dpicken/atari-hw/pdf/gtia-interposer-layout.pdf

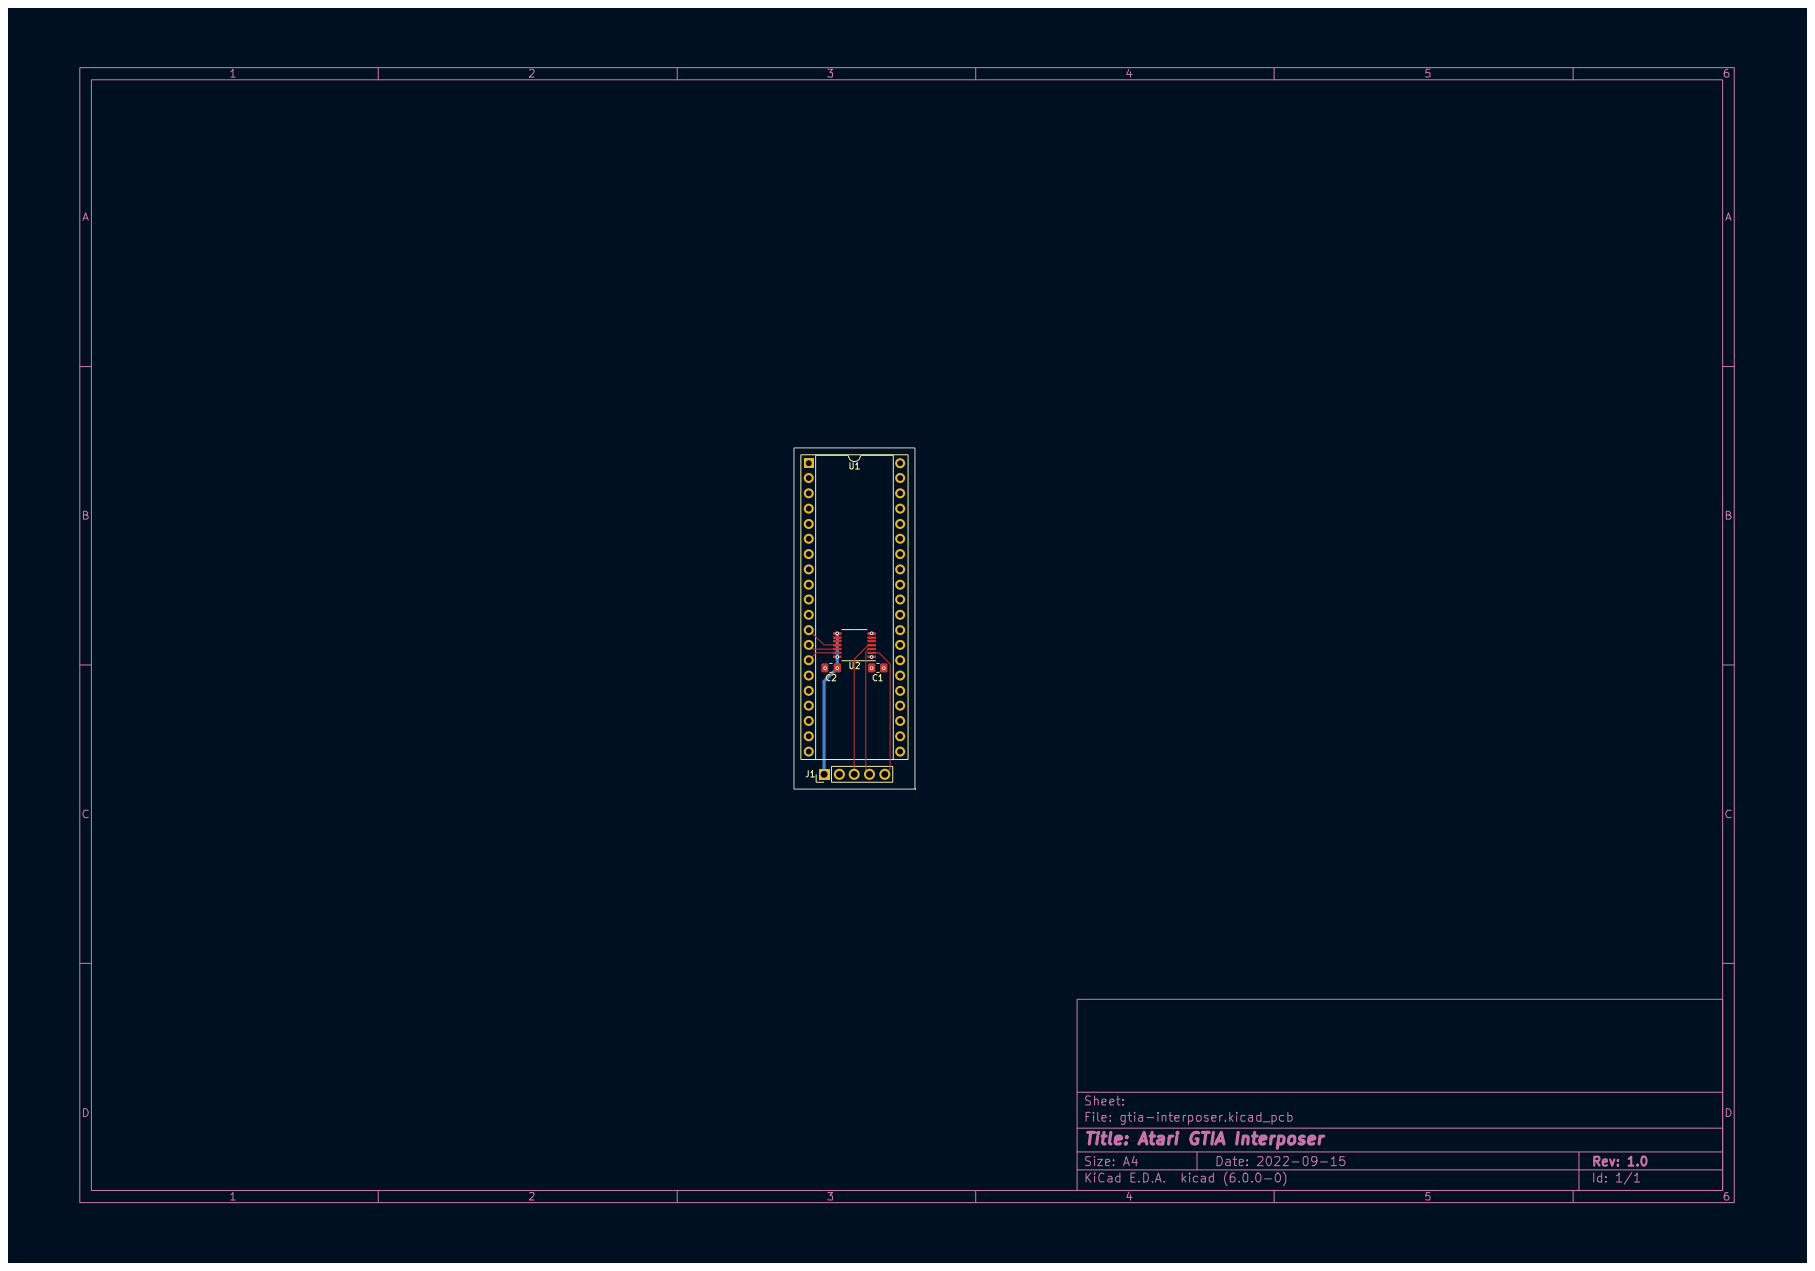
[picture p34: page 1]
