dpicken/atari-hw/pdf/pokey-interposer-layout.pdf

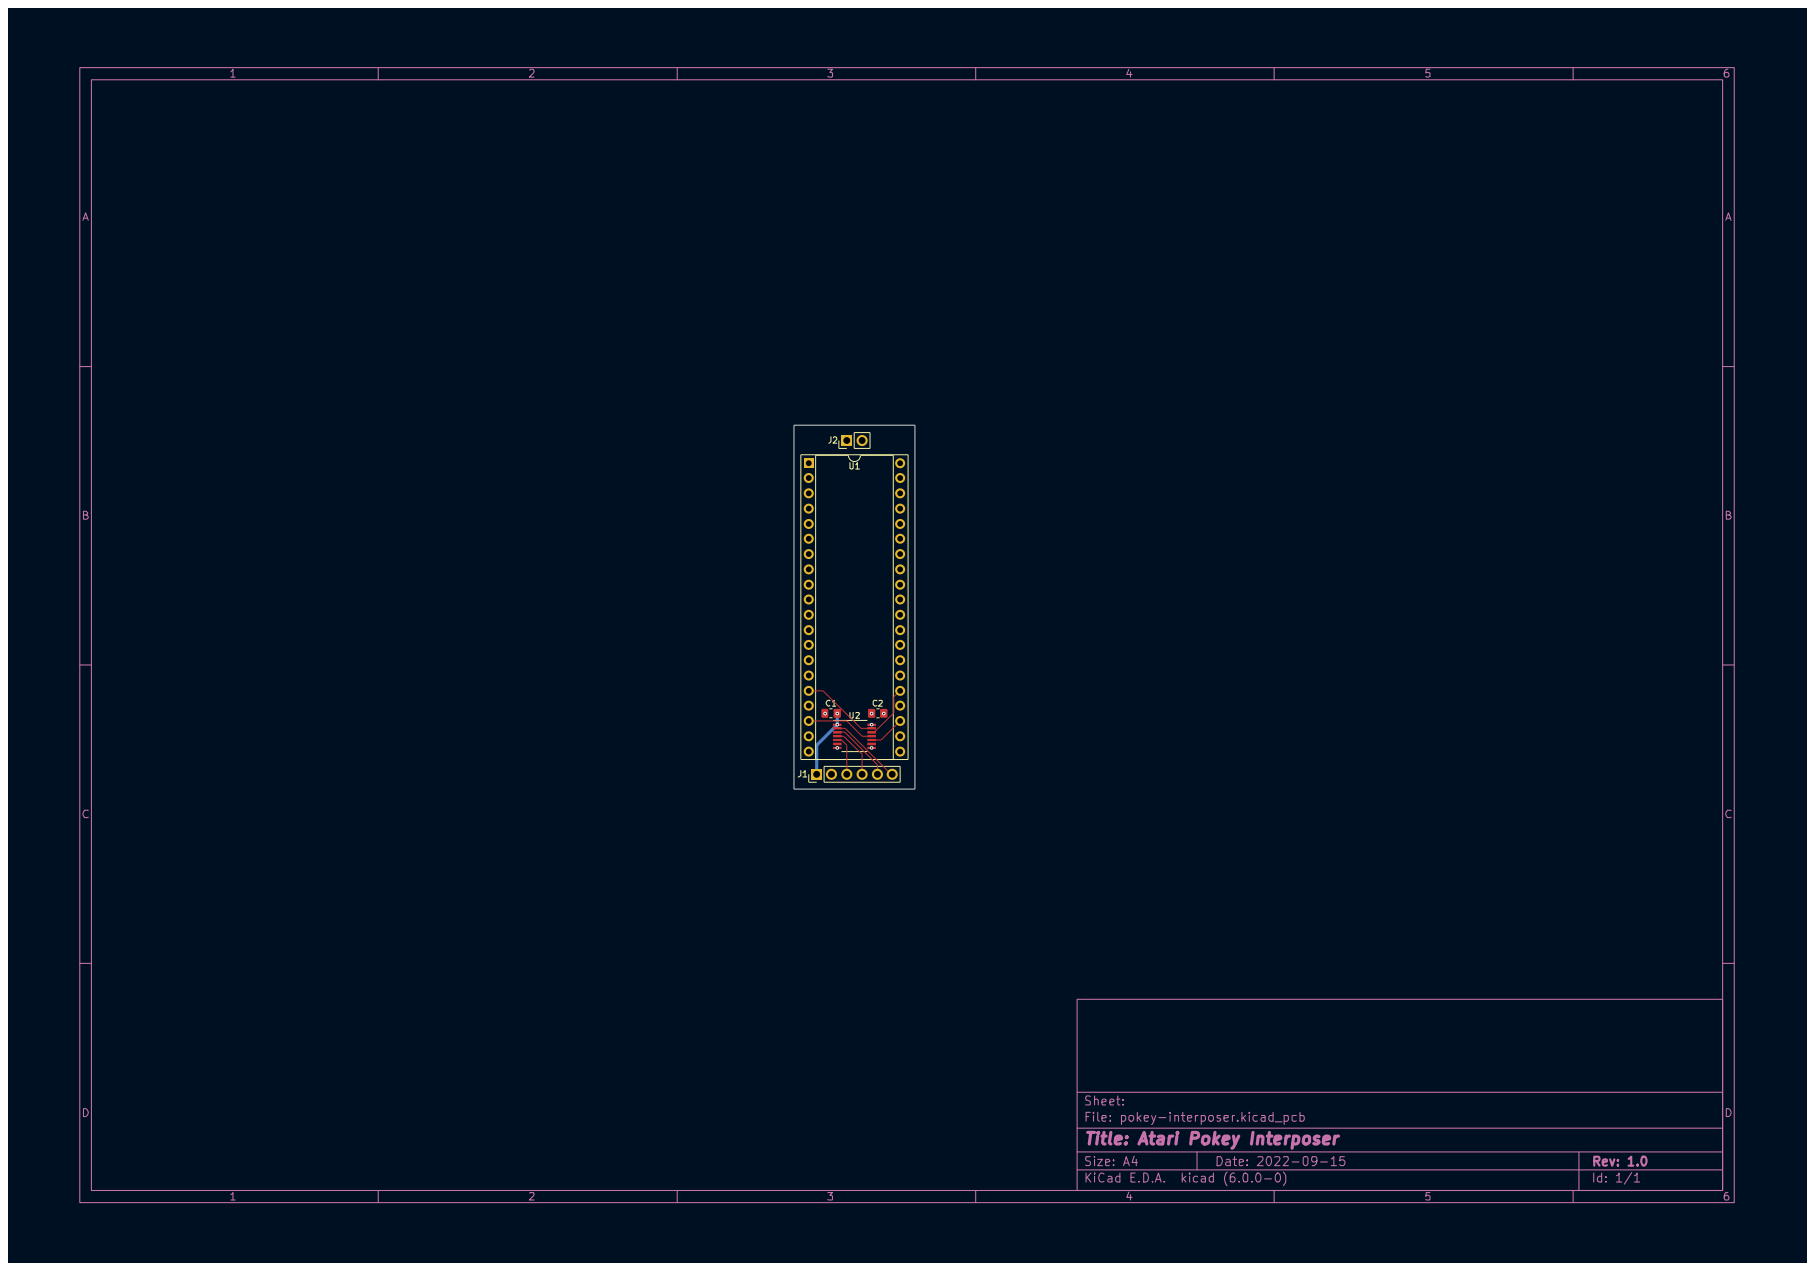
[picture p35: page 1]
